paolorussian/lostClock/stl/frameBar.stl

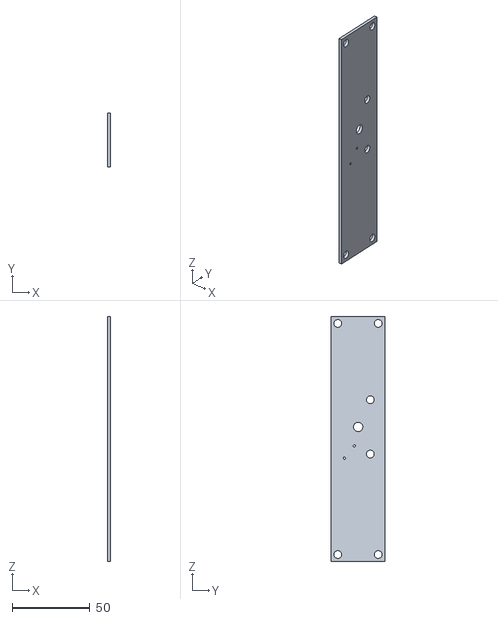
[picture p17: CAD file, 2021-06-15]
stl/frameBar.stl
2.00 x 35.0 x 158.0
